AmriteshKr8/espwatch/espwatch_final/JetBrainsMono_ExtraBold14pt7b.h

const uint8_t JetBrainsMono_ExtraBold14pt7bBitmaps[] PROGMEM = {
  0x00, 0xF7, 0xBD, 0xEF, 0x7B, 0xDE, 0xF7, 0x9C, 0xE7, 0x00, 0x00, 0xFF,
  0xFC, 0xF3, 0xFC, 0xFF, 0x3F, 0xCF, 0xF3, 0xFC, 0xFF, 0x1F, 0xC7, 0x0E,
  0x1C, 0x1C, 0x70, 0x38, 0xE0, 0x71, 0xCF, 0xFF, 0xFF, 0xFF, 0xFF, 0xFF,
  0x8E, 0x38, 0x1C, 0x70, 0x38, 0xE0, 0xE1, 0xC1, 0xC3, 0x0F, 0xFF, 0xDF,
  0xFF, 0xBF, 0xFF, 0x1C, 0x70, 0x70, 0xE0, 0xE1, 0x81, 0xC7, 0x00, 0x03,
  0x00, 0x0C, 0x00, 0x30, 0x01, 0xE0, 0x3F, 0xF1, 0xFF, 0xE7, 0xFF, 0x9C,
  0xCF, 0xF3, 0x03, 0xEC, 0x07, 0xF0, 0x1F, 0xF0, 0x3F, 0xF0, 0x3F, 0xE0,
  0x3F, 0xC0, 0xDF, 0x03, 0x3F, 0xCC, 0xFF, 0xB3, 0xDF, 0xFF, 0x7F, 0xF8,
  0xFF, 0xC0, 0xFE, 0x00, 0xC0, 0x03, 0x00, 0x0C, 0x00, 0x30, 0x00, 0x3C,
  0x01, 0xFC, 0x03, 0x9C, 0x07, 0x38, 0x0E, 0x70, 0x3C, 0xE1, 0xFF, 0x8F,
  0x1E, 0x38, 0x01, 0xE0, 0x0F, 0x00, 0x38, 0x01, 0xE7, 0xCF, 0x1F, 0xD8,
  0x31, 0xA0, 0x63, 0x80, 0xC7, 0x01, 0xDC, 0x03, 0xF8, 0x03, 0xE0, 0x07,
  0xC0, 0x3F, 0xC0, 0xFF, 0xC1, 0xFF, 0xC3, 0x87, 0x87, 0x00, 0x0F, 0x00,
  0x0F, 0x00, 0x7E, 0x01, 0xFE, 0x3F, 0xDE, 0xF7, 0x9F, 0xCF, 0x1F, 0x9E,
  0x3E, 0x3C, 0x3C, 0x7F, 0xFC, 0x7F, 0xF8, 0xFF, 0xF8, 0x7C, 0x78, 0xFF,
  0xFF, 0xFF, 0xF7, 0x01, 0x83, 0xC3, 0xE3, 0xF3, 0xF3, 0xE1, 0xE0, 0xF0,
  0xF8, 0x78, 0x3C, 0x1E, 0x0F, 0x07, 0x83, 0xC1, 0xE0, 0xF0, 0x7C, 0x1E,
  0x0F, 0x07, 0xC1, 0xF0, 0x7E, 0x3F, 0x07, 0x80, 0xC0, 0xC0, 0x78, 0x3E,
  0x1F, 0xC3, 0xE0, 0xF8, 0x3C, 0x1F, 0x07, 0x83, 0xC1, 0xE0, 0xF0, 0x78,
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
  {  1055,  14,  19,  16,    1,  -18 },   // 0x47 'G'
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

const GFXfont JetBrainsMono_ExtraBold14pt7b PROGMEM = {
  (uint8_t  *)JetBrainsMono_ExtraBold14pt7bBitmaps,
  (GFXglyph *)JetBrainsMono_ExtraBold14pt7bGlyphs,
  0x20, 0x7E, 34 };

// Approx. 3427 bytes
