AmriteshKr8/espwatch/espwatch_final/JetBrainsMono_ExtraBold16pt7b.h

const uint8_t JetBrainsMono_ExtraBold16pt7bBitmaps[] PROGMEM = {
  0x00, 0xFF, 0xFF, 0xFF, 0xFF, 0xFF, 0xFF, 0xFD, 0xEF, 0x39, 0xC0, 0x00,
  0x01, 0xFF, 0xFF, 0xC0, 0xF8, 0xFF, 0x8F, 0xF8, 0xFF, 0x8F, 0xF8, 0xFF,
  0x8F, 0x78, 0xF7, 0x8F, 0x78, 0xF7, 0x8F, 0x07, 0x0F, 0x03, 0x87, 0x01,
  0xC3, 0x81, 0xE1, 0xC0, 0xF1, 0xE3, 0xFF, 0xFD, 0xFF, 0xFE, 0xFF, 0xFF,
  0x0E, 0x1C, 0x0F, 0x0E, 0x07, 0x8F, 0x03, 0x87, 0x81, 0xC3, 0x80, 0xE1,
  0xC3, 0xFF, 0xFD, 0xFF, 0xFE, 0xFF, 0xFF, 0x1C, 0x3C, 0x0E, 0x1C, 0x07,
  0x0E, 0x03, 0x87, 0x03, 0xC3, 0x81, 0xE3, 0xC0, 0x01, 0x80, 0x01, 0x80,
  0x01, 0x80, 0x01, 0x80, 0x07, 0xF0, 0x1F, 0xFC, 0x3F, 0xFE, 0x7F, 0xFE,
  0x7D, 0xBF, 0x79, 0x9F, 0x79, 0x80, 0x79, 0x80, 0x7D, 0x80, 0x7F, 0x80,
  0x3F, 0xF0, 0x1F, 0xFC, 0x0F, 0xFE, 0x01, 0xFF, 0x01, 0xBF, 0x01, 0x8F,
  0x01, 0x8F, 0xF9, 0x8F, 0x79, 0x8F, 0x7F, 0x9F, 0x7F, 0xFF, 0x3F, 0xFE,
  0x1F, 0xFC, 0x07, 0xF0, 0x01, 0x80, 0x01, 0x80, 0x01, 0x80, 0x01, 0x80,
  0x3E, 0x00, 0x3F, 0x80, 0x3F, 0xE0, 0x1C, 0x70, 0x0E, 0x38, 0x07, 0x1C,
  0x07, 0x8E, 0x0F, 0xFF, 0x0F, 0x7F, 0x1E, 0x1F, 0x1E, 0x00, 0x3C, 0x00,
  0x78, 0x00, 0x78, 0x00, 0xF1, 0xF0, 0xF3, 0xFD, 0xE1, 0xFE, 0xC0, 0xE7,
  0xC0, 0x71, 0xC0, 0x38, 0xE0, 0x1C, 0xF0, 0x0F, 0xF0, 0x07, 0xF8, 0x00,
  0xF0, 0x03, 0xE0, 0x07, 0xFC, 0x07, 0xFF, 0x07, 0xFF, 0x83, 0xE3, 0xE1,
  0xE1, 0xF0, 0xF0, 0x00, 0x7C, 0x00, 0x1E, 0x00, 0x1F, 0x80, 0x1F, 0xE0,
  0x0F, 0xF1, 0xFF, 0xBC, 0xF7, 0xDF, 0xFB, 0xC7, 0xF9, 0xE1, 0xFC, 0xF0,
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
  {  1437,  16,  23,  19,    1,  -22 },   // 0x47 'G'
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

const GFXfont JetBrainsMono_ExtraBold16pt7b PROGMEM = {
  (uint8_t  *)JetBrainsMono_ExtraBold16pt7bBitmaps,
  (GFXglyph *)JetBrainsMono_ExtraBold16pt7bGlyphs,
  0x20, 0x7E, 39 };

// Approx. 4423 bytes
