AmriteshKr8/espwatch/espwatch_final/JetBrainsMono_ExtraBold18pt7b.h

const uint8_t JetBrainsMono_ExtraBold18pt7bBitmaps[] PROGMEM = {
  0x00, 0x7C, 0xF9, 0xF3, 0xE7, 0xCF, 0x9F, 0x3E, 0x7C, 0xF9, 0xF3, 0xE7,
  0xCF, 0x9F, 0x3E, 0x3C, 0x00, 0x00, 0x00, 0x07, 0x1F, 0x7F, 0x7E, 0xF8,
  0xF8, 0xFF, 0xC7, 0xFE, 0x3F, 0xF1, 0xFF, 0x8F, 0xFC, 0x7F, 0xE3, 0xFF,
  0x1F, 0xF8, 0xFF, 0xC7, 0xFE, 0x3E, 0x03, 0xC3, 0xC0, 0x70, 0x70, 0x1E,
  0x0E, 0x03, 0xC3, 0xC0, 0x78, 0x78, 0x0F, 0x0F, 0x1F, 0xFF, 0xFB, 0xFF,
  0xFF, 0x7F, 0xFF, 0xEF, 0xFF, 0xFC, 0x3C, 0x3C, 0x07, 0x87, 0x80, 0xE0,
  0xF0, 0x1C, 0x1C, 0x07, 0x87, 0x80, 0xF0, 0xF0, 0xFF, 0xFF, 0xDF, 0xFF,
  0xFB, 0xFF, 0xFF, 0x7F, 0xFF, 0xE3, 0xC1, 0xC0, 0x78, 0x78, 0x0F, 0x0F,
  0x01, 0xE1, 0xE0, 0x38, 0x3C, 0x0F, 0x07, 0x00, 0x01, 0x80, 0x00, 0x60,
  0x00, 0x18, 0x00, 0x06, 0x00, 0x07, 0xF0, 0x07, 0xFF, 0x03, 0xFF, 0xE1,
  0xFF, 0xFC, 0xFD, 0xBF, 0xBE, 0x67, 0xEF, 0x98, 0xFB, 0xE6, 0x00, 0xF9,
  0x80, 0x3F, 0x60, 0x07, 0xFC, 0x01, 0xFF, 0xE0, 0x3F, 0xFE, 0x03, 0xFF,
  0xC0, 0x3F, 0xF8, 0x06, 0xFE, 0x01, 0x8F, 0x80, 0x63, 0xFF, 0x98, 0x7F,
  0xE6, 0x3E, 0xFD, 0x8F, 0xBF, 0xFF, 0xE7, 0xFF, 0xF0, 0xFF, 0xFC, 0x1F,
  0xFC, 0x01, 0xFE, 0x00, 0x18, 0x00, 0x06, 0x00, 0x01, 0x80, 0x00, 0x60,
  0x00, 0x18, 0x00, 0x1F, 0x00, 0x0F, 0xF0, 0x01, 0xFF, 0x00, 0x78, 0xE0,
  0x0F, 0x1C, 0x01, 0xE3, 0x80, 0x3C, 0x70, 0x0F, 0x8E, 0x07, 0x7F, 0xC3,
  0xEF, 0xF0, 0xF0, 0x7C, 0x7C, 0x00, 0x1E, 0x00, 0x0F, 0x80, 0x03, 0xC0,
  0x01, 0xE0, 0x00, 0xF8, 0xF8, 0x3C, 0x3F, 0xDF, 0x0F, 0xFB, 0x81, 0xE7,
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
  {  1823,  17,  26,  21,    2,  -25 },   // 0x47 'G'
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

const GFXfont JetBrainsMono_ExtraBold18pt7b PROGMEM = {
  (uint8_t  *)JetBrainsMono_ExtraBold18pt7bBitmaps,
  (GFXglyph *)JetBrainsMono_ExtraBold18pt7bGlyphs,
  0x20, 0x7E, 44 };

// Approx. 5409 bytes
