AmriteshKr8/espwatch/espwatch_final/JetBrainsMono_ExtraBold24pt7b.h

const uint8_t JetBrainsMono_ExtraBold24pt7bBitmaps[] PROGMEM = {
  0x00, 0xFF, 0xFF, 0xFF, 0xFF, 0xFF, 0xFF, 0xFF, 0xFF, 0x7F, 0x7F, 0x7F,
  0x7E, 0x7E, 0x7E, 0x7E, 0x7E, 0x7E, 0x7E, 0x7E, 0x7E, 0x7E, 0x7E, 0x00,
  0x00, 0x00, 0x00, 0x00, 0x7E, 0xFF, 0xFF, 0xFF, 0xFF, 0x7E, 0xFE, 0x1F,
  0xFF, 0x87, 0xFF, 0xE1, 0xFF, 0xF8, 0x7F, 0xFE, 0x1F, 0xFF, 0x87, 0xFF,
  0xE1, 0xFF, 0xF8, 0x7F, 0xFE, 0x1F, 0xFF, 0x87, 0xFF, 0xE1, 0xFD, 0xF8,
  0x7F, 0x7E, 0x0F, 0xDF, 0x83, 0xE0, 0x00, 0xF8, 0x1F, 0x00, 0x3E, 0x07,
  0xC0, 0x0F, 0x83, 0xE0, 0x07, 0xC0, 0xF8, 0x01, 0xF0, 0x3E, 0x00, 0x7C,
  0x0F, 0x80, 0x1F, 0x03, 0xE0, 0xFF, 0xFF, 0xFF, 0x3F, 0xFF, 0xFF, 0xCF,
  0xFF, 0xFF, 0xF3, 0xFF, 0xFF, 0xFC, 0xFF, 0xFF, 0xFF, 0x03, 0xE0, 0x7C,
  0x00, 0xF8, 0x3E, 0x00, 0x7C, 0x0F, 0x80, 0x1F, 0x03, 0xE0, 0x07, 0xC0,
  0xF8, 0x01, 0xF0, 0x3E, 0x00, 0x7C, 0x0F, 0x80, 0x1F, 0x07, 0xC0, 0xFF,
  0xFF, 0xFF, 0xBF, 0xFF, 0xFF, 0xEF, 0xFF, 0xFF, 0xFB, 0xFF, 0xFF, 0xFE,
  0xFF, 0xFF, 0xFF, 0x83, 0xE0, 0xF8, 0x01, 0xF0, 0x3E, 0x00, 0x7C, 0x0F,
  0x80, 0x1F, 0x03, 0xE0, 0x07, 0xC0, 0xF8, 0x01, 0xF0, 0x3C, 0x00, 0x78,
  0x1F, 0x00, 0x3E, 0x07, 0xC0, 0x00, 0x00, 0x38, 0x00, 0x00, 0x38, 0x00,
  0x00, 0x38, 0x00, 0x00, 0x38, 0x00, 0x00, 0x38, 0x00, 0x00, 0x38, 0x00,
  0x03, 0xFF, 0xC0, 0x0F, 0xFF, 0xE0, 0x1F, 0xFF, 0xF8, 0x3F, 0xFF, 0xFC,
  0x3F, 0xFF, 0xFC, 0x7F, 0xBB, 0xFE, 0x7F, 0x38, 0xFE, 0x7E, 0x38, 0xFE,
  0xFE, 0x38, 0x7F, 0xFE, 0x38, 0x00, 0x7E, 0x38, 0x00, 0x7F, 0x38, 0x00,
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
  {  3089,  24,  33,  28,    2,  -32 },   // 0x47 'G'
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

const GFXfont JetBrainsMono_ExtraBold24pt7b PROGMEM = {
  (uint8_t  *)JetBrainsMono_ExtraBold24pt7bBitmaps,
  (GFXglyph *)JetBrainsMono_ExtraBold24pt7bGlyphs,
  0x20, 0x7E, 58 };

// Approx. 8727 bytes
