AmriteshKr8/espwatch/espwatch_final/JetBrainsMono_ExtraBold30pt7b.h

const uint8_t JetBrainsMono_ExtraBold30pt7bBitmaps[] PROGMEM = {
  0x00, 0x7F, 0xCF, 0xF9, 0xFF, 0x3F, 0xE7, 0xFC, 0xFF, 0x9F, 0xF3, 0xFE,
  0x7F, 0xCF, 0xF9, 0xFF, 0x3F, 0xE7, 0xFC, 0xFF, 0x9F, 0xF3, 0xFE, 0x3F,
  0xC7, 0xF8, 0xFF, 0x1F, 0xE3, 0xF8, 0x7F, 0x0F, 0xE1, 0xFC, 0x3F, 0x87,
  0xF0, 0xFE, 0x1F, 0xC0, 0x00, 0x00, 0x00, 0x00, 0x00, 0x00, 0x00, 0x00,
  0x3C, 0x3F, 0xE7, 0xFF, 0xFF, 0xFF, 0xFB, 0xFF, 0x7F, 0xC7, 0xF0, 0xFF,
  0x83, 0xFF, 0xFF, 0x07, 0xFF, 0xFE, 0x0F, 0xFF, 0xFC, 0x1F, 0xFF, 0xF8,
  0x3F, 0xFF, 0xF0, 0x7F, 0xFF, 0xE0, 0xFF, 0xFF, 0xC1, 0xFF, 0xFF, 0x83,
  0xFF, 0xFF, 0x07, 0xFD, 0xFE, 0x0F, 0xFB, 0xFC, 0x1F, 0xF7, 0xF8, 0x3F,
  0xEF, 0xF0, 0x7F, 0x9F, 0xE0, 0x7F, 0x3F, 0xC0, 0xFE, 0x7F, 0x81, 0xFC,
  0xFE, 0x03, 0xF8, 0x00, 0x3F, 0x80, 0xFC, 0x00, 0x1F, 0x80, 0x7E, 0x00,
  0x0F, 0xC0, 0x3F, 0x00, 0x07, 0xE0, 0x3F, 0x80, 0x03, 0xF0, 0x1F, 0x80,
  0x03, 0xF8, 0x0F, 0xC0, 0x01, 0xF8, 0x07, 0xE0, 0x00, 0xFC, 0x03, 0xF0,
  0x00, 0x7E, 0x03, 0xF8, 0x00, 0x3F, 0x01, 0xF8, 0x0F, 0xFF, 0xFF, 0xFF,
  0xE7, 0xFF, 0xFF, 0xFF, 0xF3, 0xFF, 0xFF, 0xFF, 0xF9, 0xFF, 0xFF, 0xFF,
  0xFC, 0xFF, 0xFF, 0xFF, 0xFE, 0x7F, 0xFF, 0xFF, 0xFF, 0x00, 0xFC, 0x07,
  0xE0, 0x00, 0xFE, 0x03, 0xF0, 0x00, 0x7E, 0x01, 0xF8, 0x00, 0x3F, 0x00,
  0xFC, 0x00, 0x1F, 0x80, 0xFE, 0x00, 0x0F, 0xC0, 0x7E, 0x00, 0x0F, 0xE0,
  0x3F, 0x00, 0x07, 0xF0, 0x1F, 0x80, 0x03, 0xF0, 0x0F, 0xC0, 0x01, 0xF8,
  0x0F, 0xE0, 0x3F, 0xFF, 0xFF, 0xFF, 0x9F, 0xFF, 0xFF, 0xFF, 0xCF, 0xFF,
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
  {  4952,  29,  43,  35,    3,  -41 },   // 0x47 'G'
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

const GFXfont JetBrainsMono_ExtraBold30pt7b PROGMEM = {
  (uint8_t  *)JetBrainsMono_ExtraBold30pt7bBitmaps,
  (GFXglyph *)JetBrainsMono_ExtraBold30pt7bGlyphs,
  0x20, 0x7E, 73 };

// Approx. 13532 bytes
